rafaellehmkuhl/Bancada-Mitica-Parts-Models/Carrinho/Eixo Linear/Eixo_Linear_12mm.SLDPRT

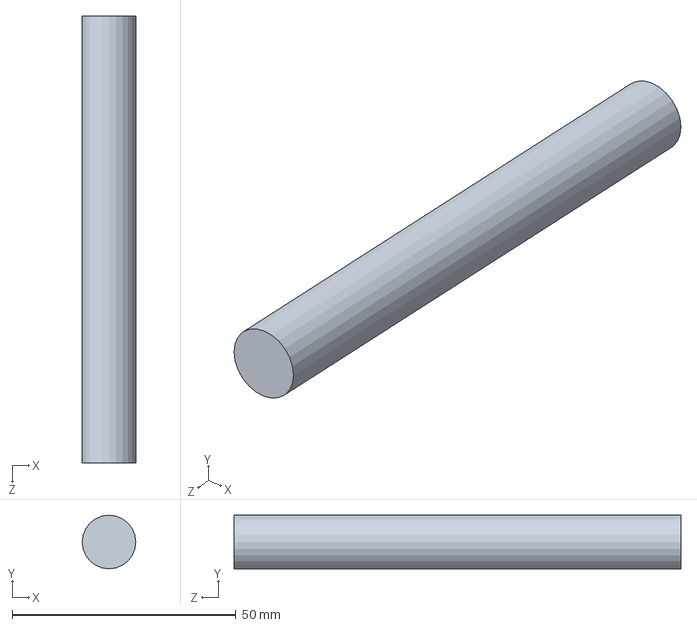
[picture p16: CAD file, 2018-05-09]
Carrinho/Eixo Linear/Eixo_Linear_12mm.SLDPRT
12.0 x 12.0 x 100.0 mm
