rafaellehmkuhl/Bancada-Mitica-Parts-Models/Carrinho/Pillow Block SC12UU/Adaptador_para_Pillow_Block_SC12UU.SLDPRT

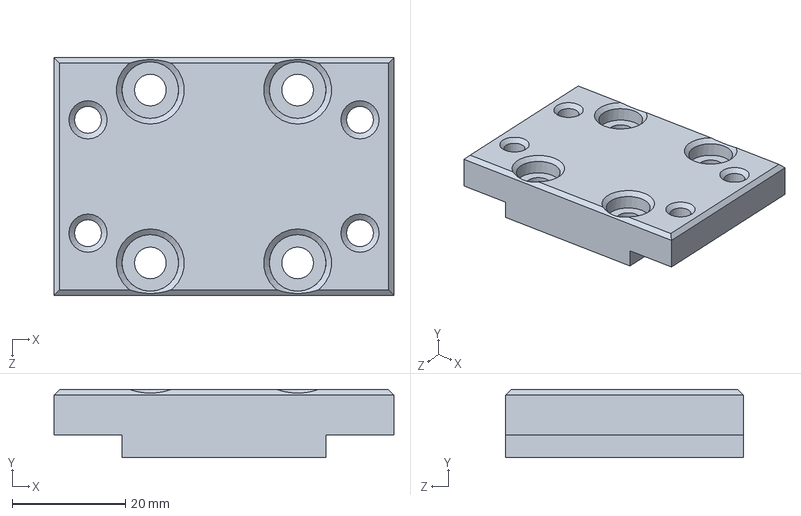
[picture p17: CAD file, 2018-05-09]
Carrinho/Pillow Block SC12UU/Adaptador_para_Pillow_Block_SC12UU.SLDPRT
60.0 x 12.0 x 42.0 mm
