rafaellehmkuhl/Bancada-Mitica-Parts-Models/Celula de carga/Encaixe_Celula - Teste de Ajuste.SLDPRT

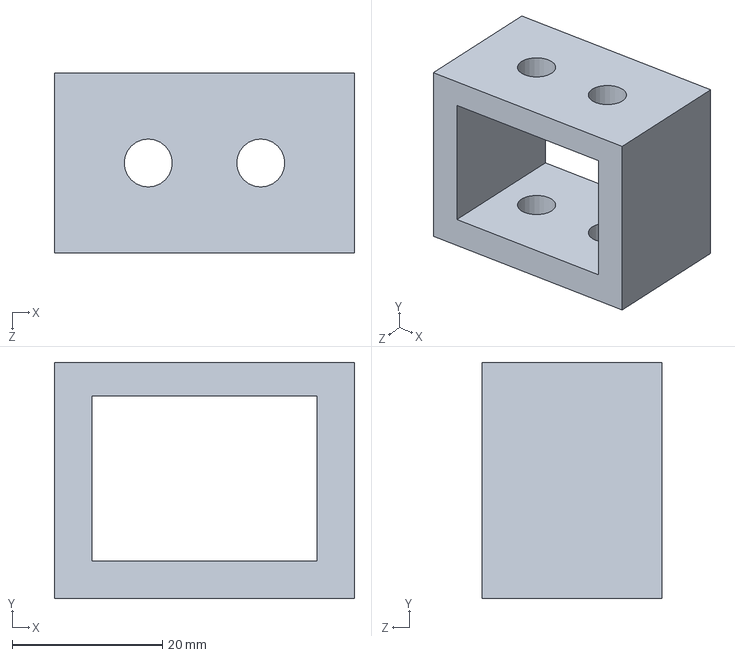
[picture p18: CAD file, 2018-07-06]
Celula de carga/Encaixe_Celula - Teste de Ajuste.SLDPRT
40.0 x 31.5 x 24.0 mm
