rafaellehmkuhl/Bancada-Mitica-Parts-Models/Celula de carga/EncaixeCelulaAnguloFixo/Encaixe_Celula_de_Angulo_Fixo.SLDPRT

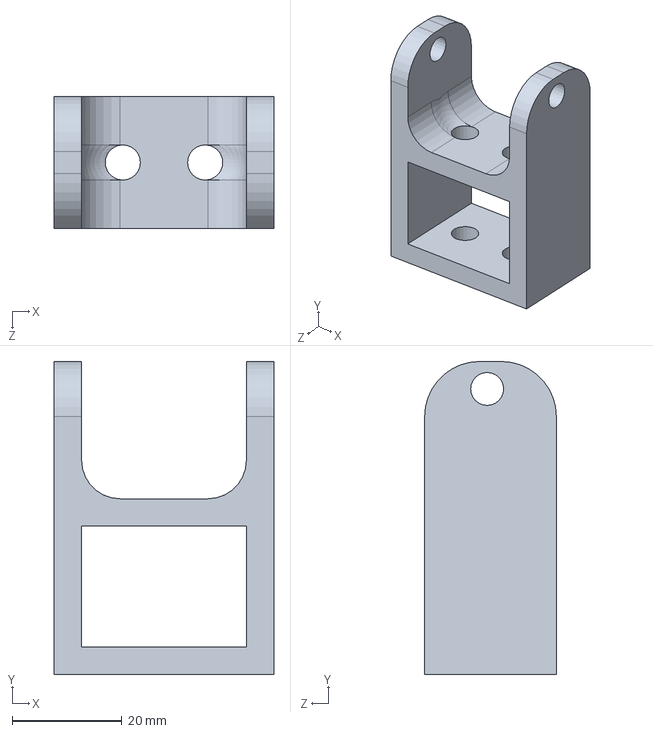
[picture p19: CAD file, 2018-07-06]
Celula de carga/EncaixeCelulaAnguloFixo/Encaixe_Celula_de_Angulo_Fixo.SLDPRT
40.0 x 57.0 x 24.0 mm
