rafaellehmkuhl/Bancada-Mitica-Parts-Models/Celula de carga/EncaixeCelulaAnguloVariavel/Peça_Central.sldprt

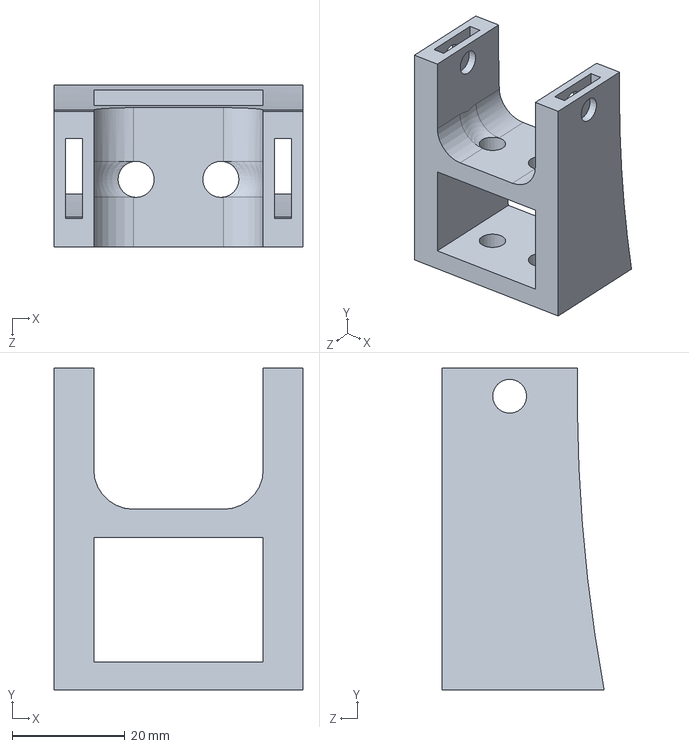
[picture p20: CAD file, 2018-07-06]
Celula de carga/EncaixeCelulaAnguloVariavel/Peça_Central.sldprt
44.0 x 57.0 x 28.7 mm
