rafaellehmkuhl/Bancada-Mitica-Parts-Models/Celula de carga/Suportes/Suporte_para_Celula_de_Carga_Reforcado_ajustavel.SLDPRT

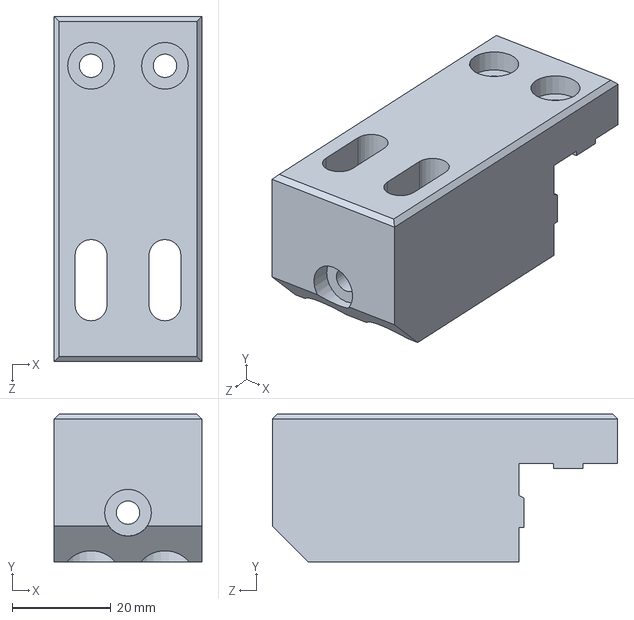
[picture p21: CAD file, 2018-07-06]
Celula de carga/Suportes/Suporte_para_Celula_de_Carga_Reforcado_ajustavel.SLDPRT
30.0 x 30.0 x 70.0 mm
