rafaellehmkuhl/Bancada-Mitica-Parts-Models/Conexoes/Antigos/AdaptadorSuporteSK12.SLDPRT

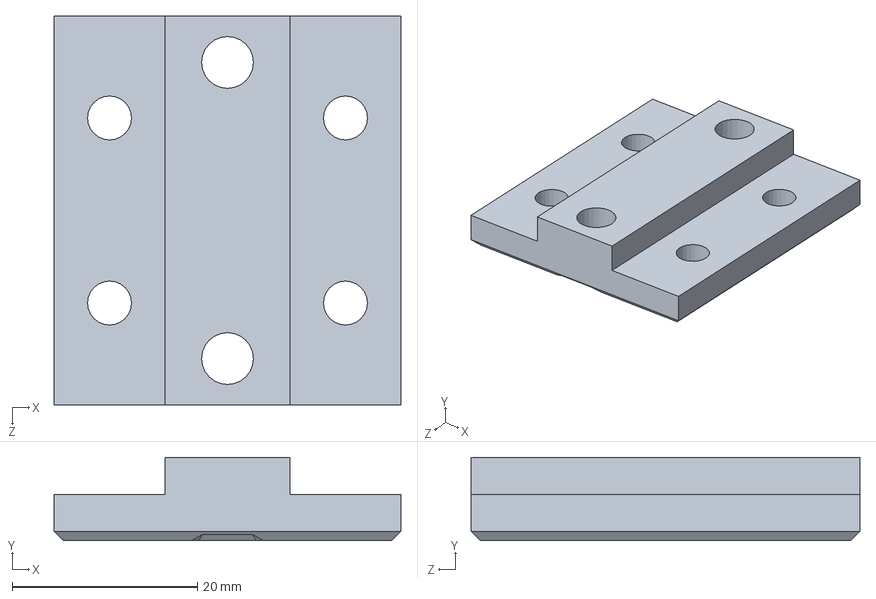
[picture p22: CAD file, 2018-04-30]
Conexoes/Antigos/AdaptadorSuporteSK12.SLDPRT
37.5 x 9.00 x 42.0 mm
