rafaellehmkuhl/Bancada-Mitica-Parts-Models/Conexoes/Cabo_de_aco.SLDPRT

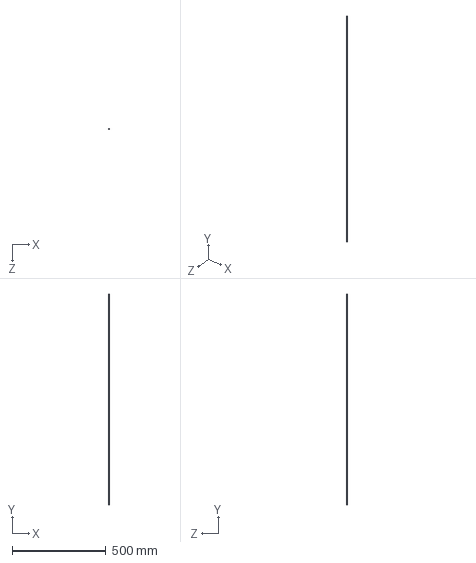
[picture p23: CAD file, 2018-05-29]
Conexoes/Cabo_de_aco.SLDPRT
6.00 x 1124.0 x 6.00 mm
