rafaellehmkuhl/Bancada-Mitica-Parts-Models/Conexoes/STLs/EncaixeDianteiroAsa.STL

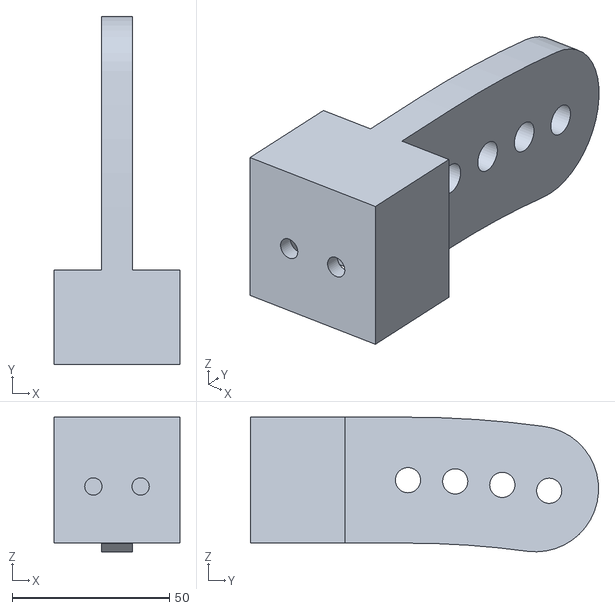
[picture p24: CAD file, 2018-07-06]
Conexoes/STLs/EncaixeDianteiroAsa.STL
40.0 x 110.5 x 42.7
