rafaellehmkuhl/Bancada-Mitica-Parts-Models/Perfis de Aluminio/Perfil_20x20mm.SLDPRT

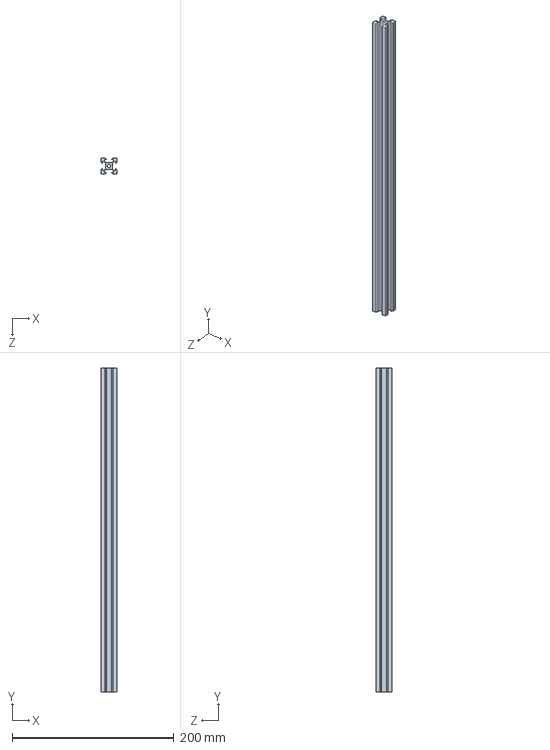
[picture p25: CAD file, 2018-05-29]
Perfis de Aluminio/Perfil_20x20mm.SLDPRT
20.0 x 400.0 x 20.0 mm
