rafaellehmkuhl/Bancada-Mitica-Parts-Models/Placas Eletronicas/Encaixe_PCBs.SLDPRT

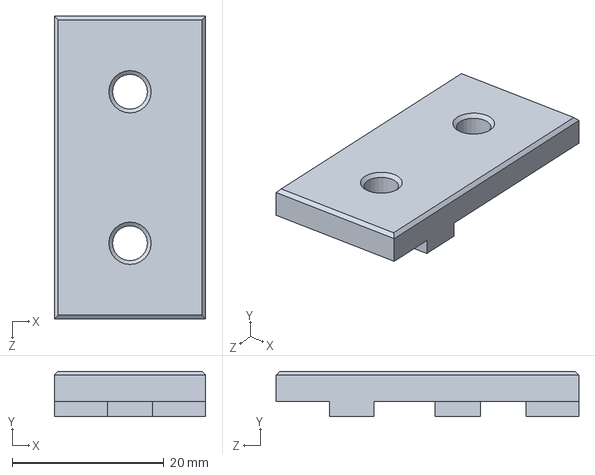
[picture p26: CAD file, 2018-04-30]
Placas Eletronicas/Encaixe_PCBs.SLDPRT
20.0 x 6.00 x 40.0 mm
