rafaellehmkuhl/Bancada-Mitica-Parts-Models/Calibraçao/Placa-asa/Abraçadeira/Abracadeira_Grampo_U_Placa_de_Calibracao_Argola.SLDPRT

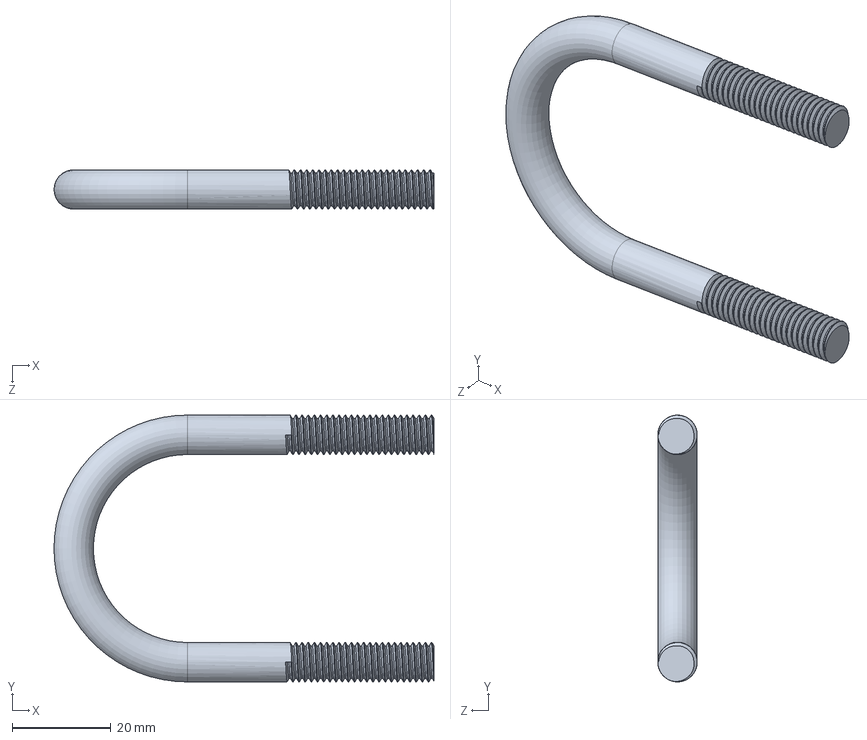
[picture p27: CAD file, 2018-07-06]
Calibraçao/Placa-asa/Abraçadeira/Abracadeira_Grampo_U_Placa_de_Calibracao_Argola.SLDPRT
77.1 x 54.1 x 8.00 mm
