rafaellehmkuhl/Bancada-Mitica-Parts-Models/Calibraçao/Placa-asa/Placa.SLDPRT

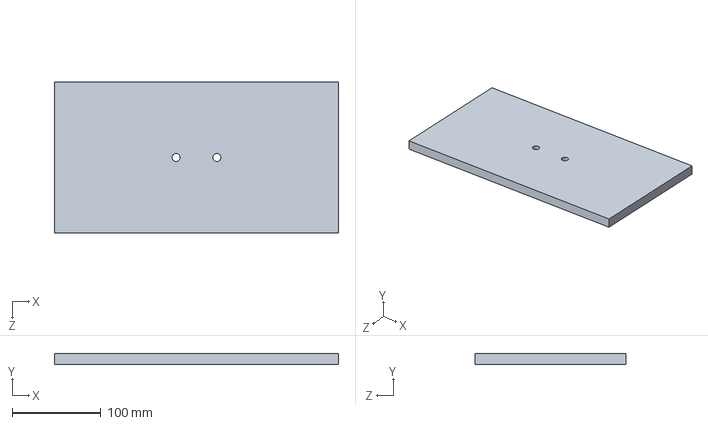
[picture p28: CAD file, 2018-07-06]
Calibraçao/Placa-asa/Placa.SLDPRT
320.0 x 12.0 x 170.0 mm
