rafaellehmkuhl/Bancada-Mitica-Parts-Models/Calibraçao/Roldana/Suporte_de_rolamento.SLDPRT

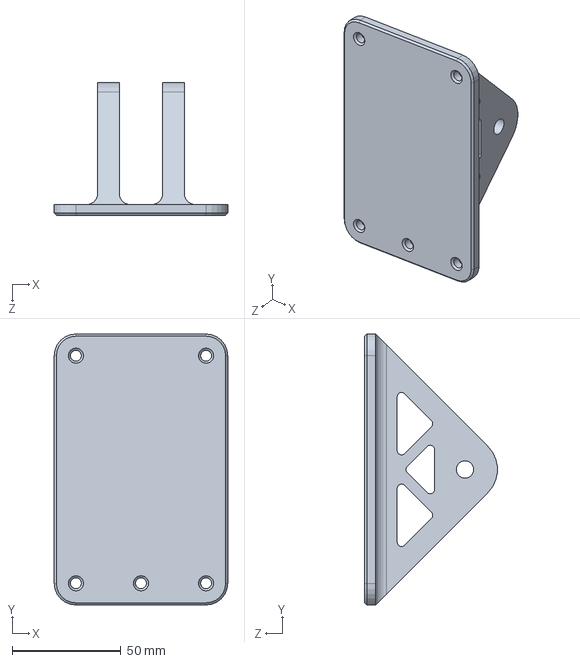
[picture p29: CAD file, 2018-05-29]
Calibraçao/Roldana/Suporte_de_rolamento.SLDPRT
80.0 x 124.9 x 61.1 mm
