rafaellehmkuhl/Bancada-Mitica-Parts-Models/Carrinho/Pillow Block SC12UU/Pillow_Block_SC12UU.SLDPRT

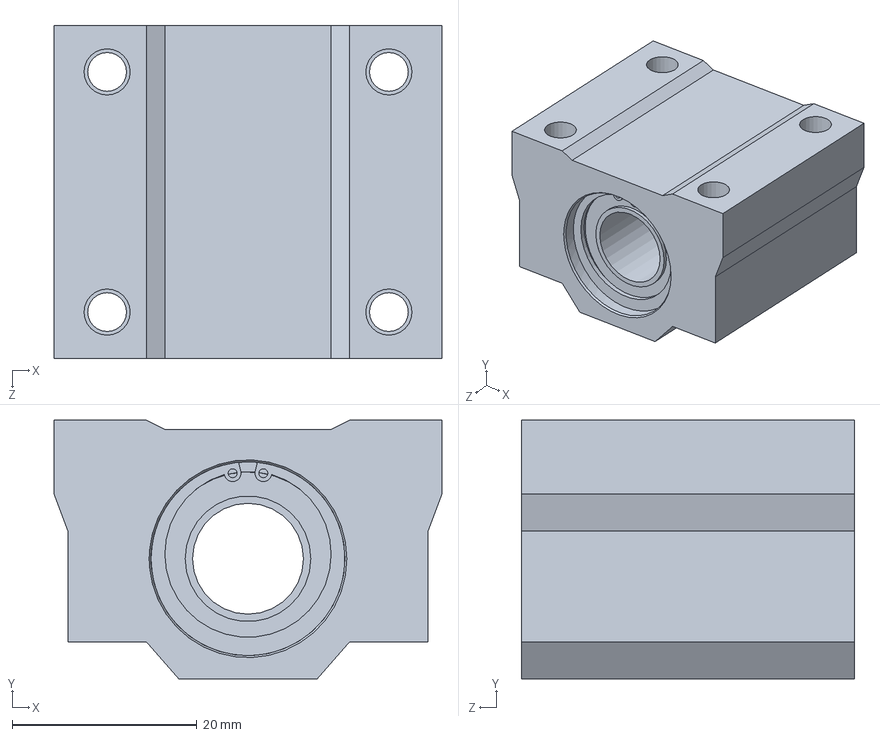
[picture p30: CAD file, 2018-05-09]
Carrinho/Pillow Block SC12UU/Pillow_Block_SC12UU.SLDPRT
42.0 x 28.0 x 36.0 mm
