rafaellehmkuhl/Bancada-Mitica-Parts-Models/Celula de carga/Celula_de_Carga_20kg.SLDPRT

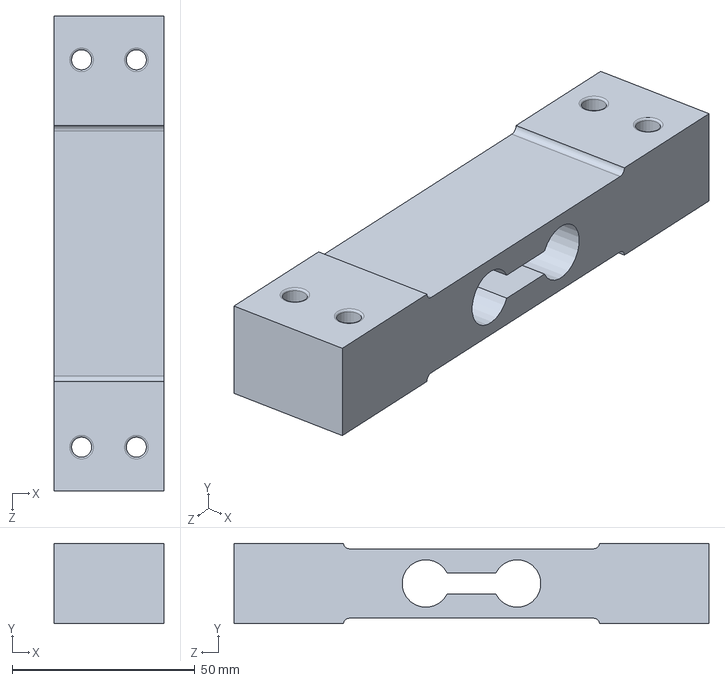
[picture p31: CAD file, 2018-05-09]
Celula de carga/Celula_de_Carga_20kg.SLDPRT
30.0 x 22.0 x 130.0 mm
