rafaellehmkuhl/Bancada-Mitica-Parts-Models/Celula de carga/EncaixeCelulaAnguloVariavel/Encaixe_Celula_de_Angulo_Variavel.SLDPRT

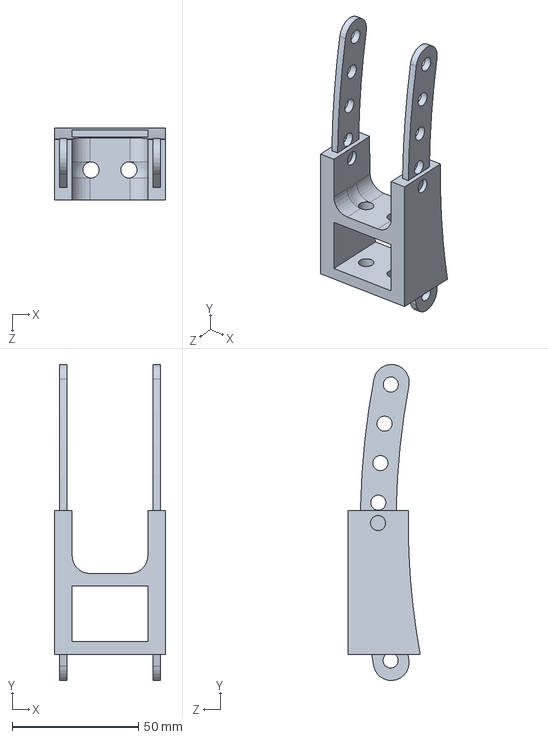
[picture p32: CAD file, 2018-07-06]
Celula de carga/EncaixeCelulaAnguloVariavel/Encaixe_Celula_de_Angulo_Variavel.SLDPRT
44.0 x 125.2 x 28.7 mm
