rafaellehmkuhl/Bancada-Mitica-Parts-Models/Celula de carga/Suportes/Suporte_para_Celula_de_Carga_Reforcado.SLDPRT

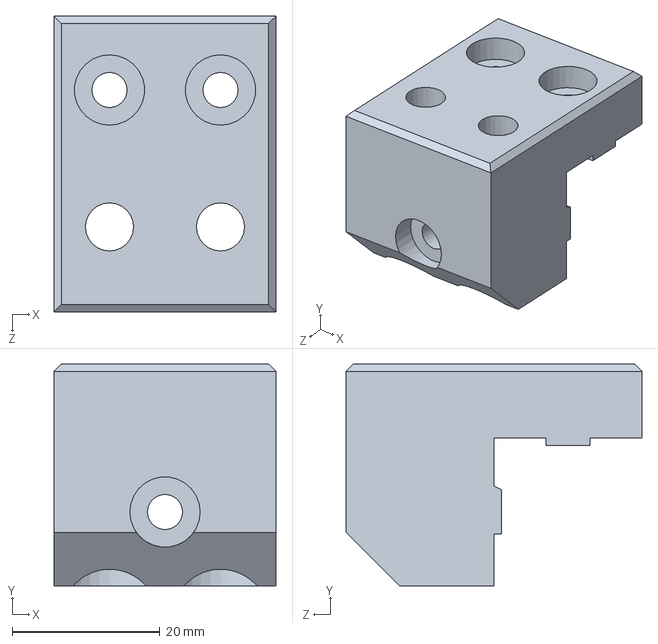
[picture p33: CAD file, 2018-05-09]
Celula de carga/Suportes/Suporte_para_Celula_de_Carga_Reforcado.SLDPRT
30.0 x 30.0 x 40.0 mm
