rafaellehmkuhl/Bancada-Mitica-Parts-Models/Conexoes/Antigos/Placa_lateral_90.SLDPRT

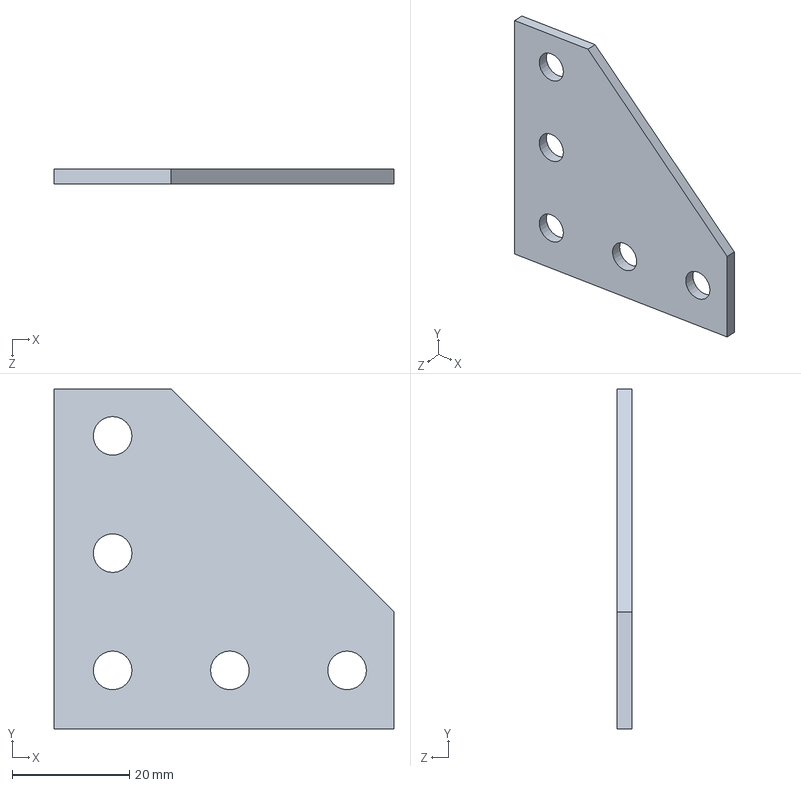
[picture p34: CAD file, 2018-04-30]
Conexoes/Antigos/Placa_lateral_90.SLDPRT
58.0 x 58.0 x 2.50 mm
