rafaellehmkuhl/Bancada-Mitica-Parts-Models/Conexoes/Parafuso_Olhal_30mm.SLDPRT

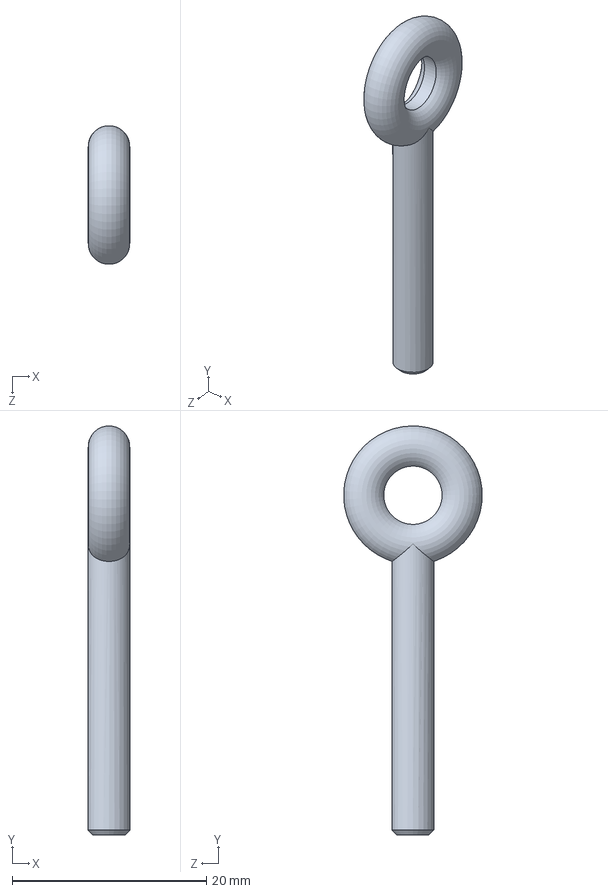
[picture p35: CAD file, 2018-05-29]
Conexoes/Parafuso_Olhal_30mm.SLDPRT
4.30 x 42.1 x 14.3 mm
