rafaellehmkuhl/Bancada-Mitica-Parts-Models/Conexoes/STLs/Placa_lateral_45.STL

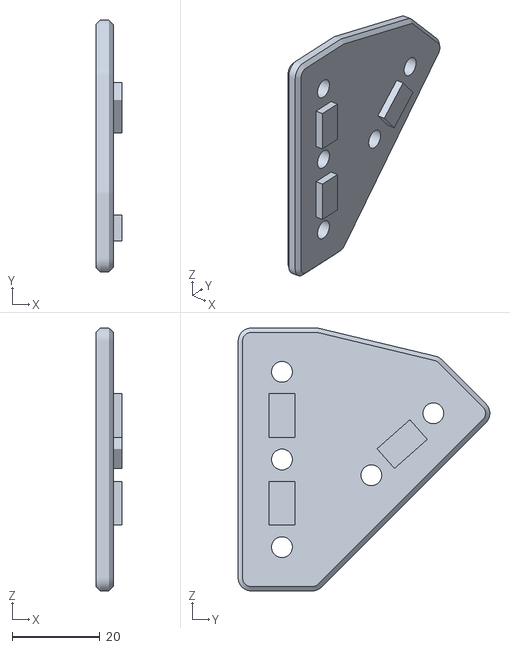
[picture p36: CAD file, 2018-04-30]
Conexoes/STLs/Placa_lateral_45.STL
6.00 x 57.4 x 60.0
