rafaellehmkuhl/Bancada-Mitica-Parts-Models/Perfis de Aluminio/Perfil_20x40mm.SLDPRT

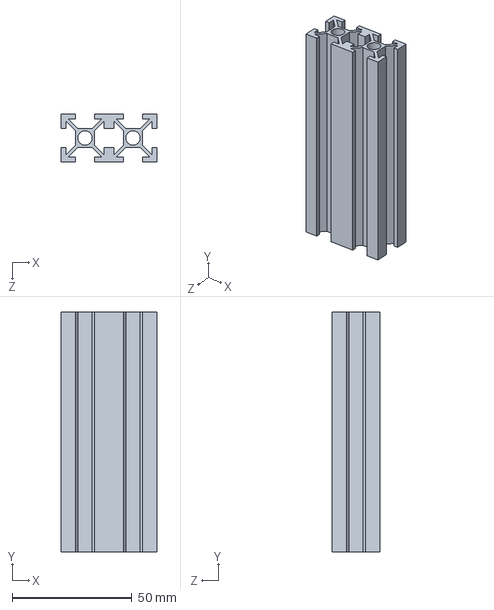
[picture p37: CAD file, 2018-05-09]
Perfis de Aluminio/Perfil_20x40mm.SLDPRT
40.0 x 100.0 x 20.0 mm
