rafaellehmkuhl/Bancada-Mitica-Parts-Models/Placas Eletronicas/Case_Celulas.SLDPRT

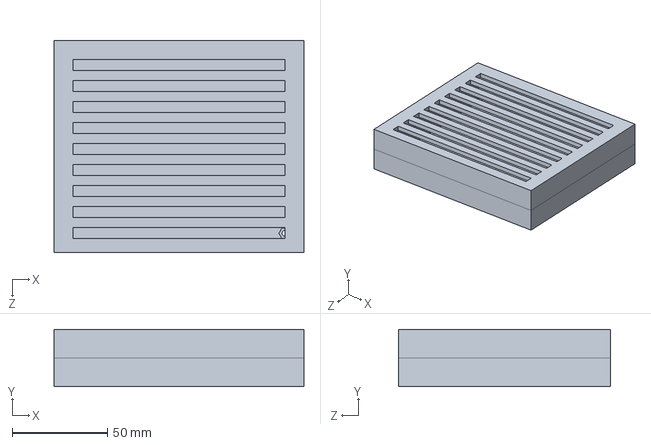
[picture p38: CAD file, 2018-04-30]
Placas Eletronicas/Case_Celulas.SLDPRT
131.0 x 30.0 x 111.0 mm
