rafaellehmkuhl/Bancada-Mitica-Parts-Models/Calibraçao/Placa-asa/Vareta6mm.SLDPRT

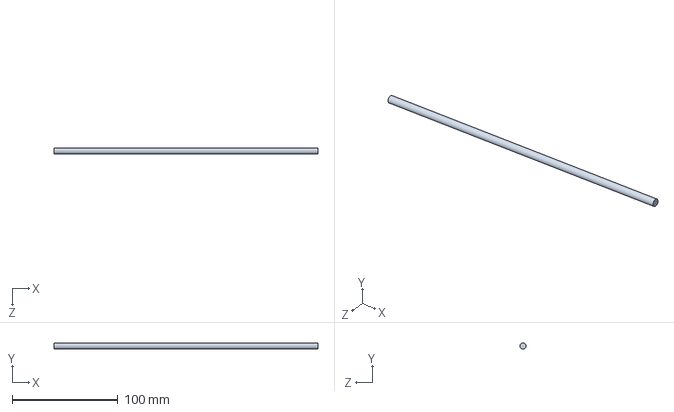
[picture p39: CAD file, 2018-07-06]
Calibraçao/Placa-asa/Vareta6mm.SLDPRT
250.0 x 6.00 x 6.00 mm
