rafaellehmkuhl/Bancada-Mitica-Parts-Models/Calibraçao/Roldana/608RS.SLDPRT

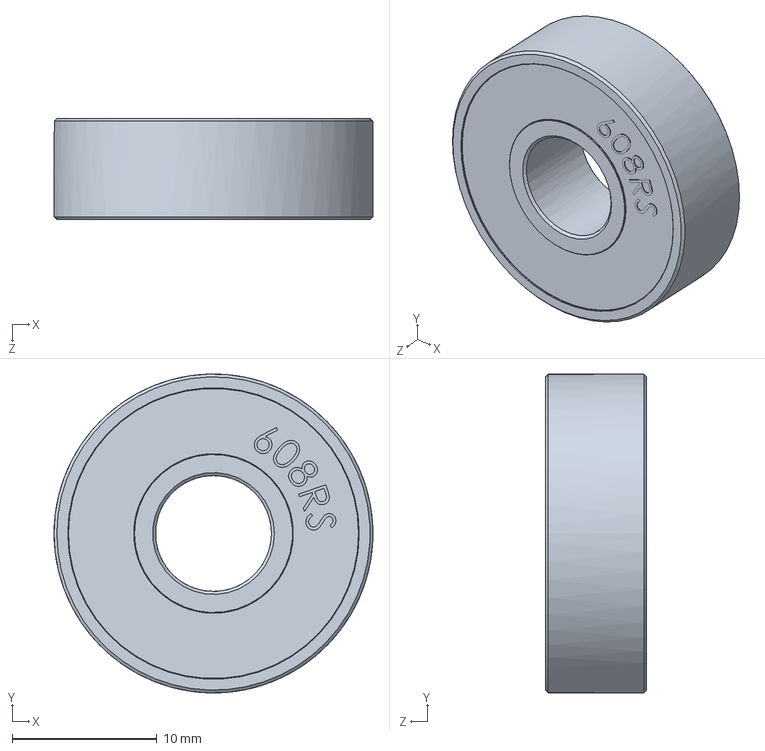
[picture p40: CAD file, 2018-05-29]
Calibraçao/Roldana/608RS.SLDPRT
22.0 x 22.0 x 7.00 mm
