rafaellehmkuhl/Bancada-Mitica-Parts-Models/Conexoes/Antigos/Placa_de_conexao_celula_de_carga.SLDPRT

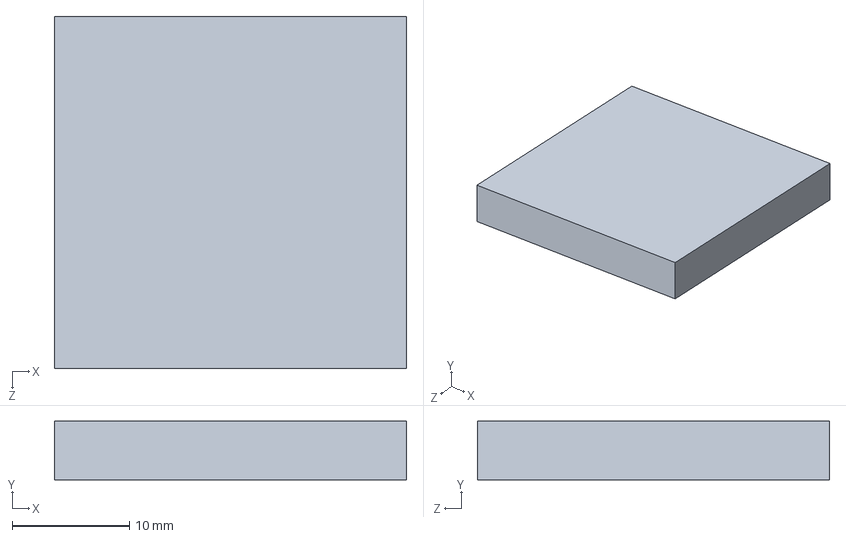
[picture p41: CAD file, 2018-04-30]
Conexoes/Antigos/Placa_de_conexao_celula_de_carga.SLDPRT
30.0 x 5.00 x 30.0 mm
