rafaellehmkuhl/Bancada-Mitica-Parts-Models/Conexoes/Cantoneira_interna_20x20mm.SLDPRT

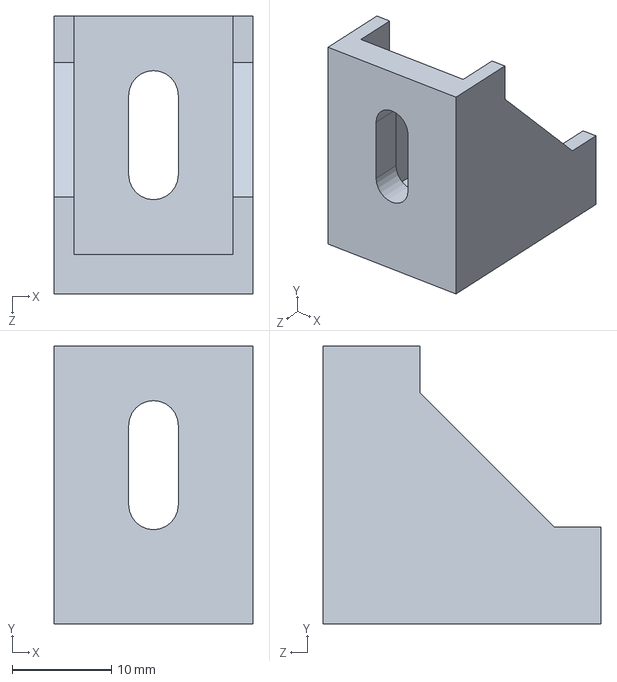
[picture p42: CAD file, 2018-05-09]
Conexoes/Cantoneira_interna_20x20mm.SLDPRT
20.0 x 28.0 x 28.0 mm
