rafaellehmkuhl/Bancada-Mitica-Parts-Models/Placas Eletronicas/Encaixe_PCBs_2.SLDPRT

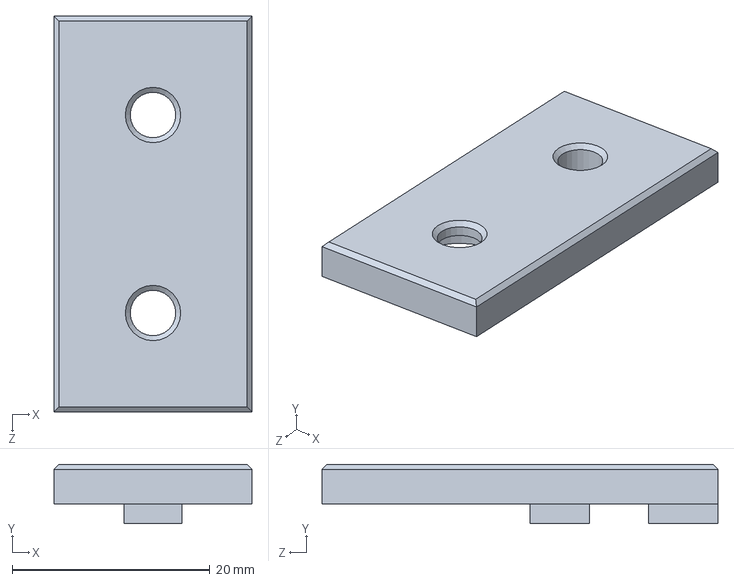
[picture p43: CAD file, 2018-04-30]
Placas Eletronicas/Encaixe_PCBs_2.SLDPRT
20.0 x 6.00 x 40.0 mm
