rafaellehmkuhl/Bancada-Mitica-Parts-Models/Calibraçao/Roldana/Encaixe_corda.SLDPRT

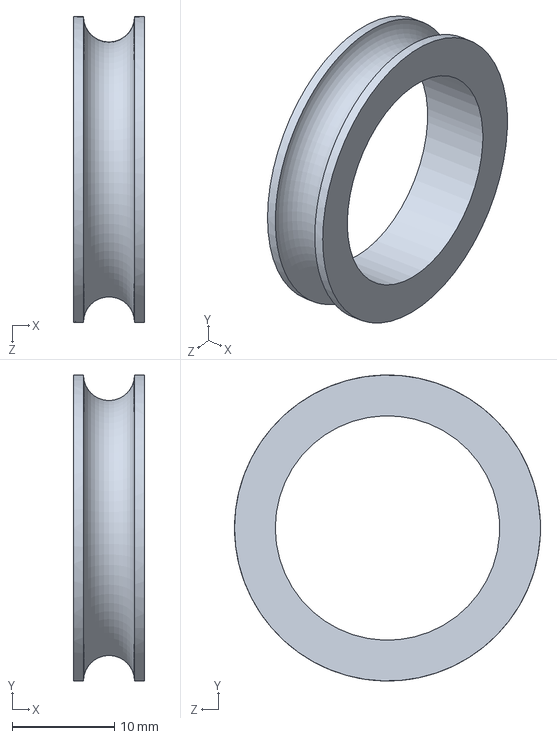
[picture p44: CAD file, 2018-05-29]
Calibraçao/Roldana/Encaixe_corda.SLDPRT
7.00 x 30.0 x 30.0 mm
