rafaellehmkuhl/Bancada-Mitica-Parts-Models/Carrinho/Pillow Block SC12UU/Rolamento_Linear_LM12UU.SLDPRT

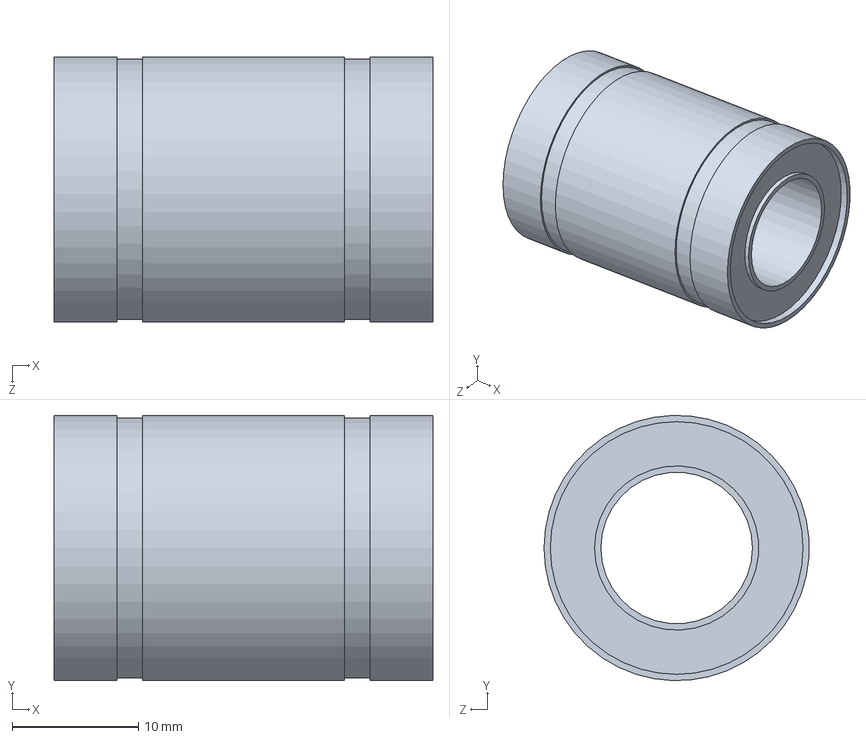
[picture p45: CAD file, 2018-04-30]
Carrinho/Pillow Block SC12UU/Rolamento_Linear_LM12UU.SLDPRT
30.0 x 21.0 x 21.0 mm
