rafaellehmkuhl/Bancada-Mitica-Parts-Models/Celula de carga/EncaixeCelulaAnguloVariavel/Peça_de_angulo.sldprt

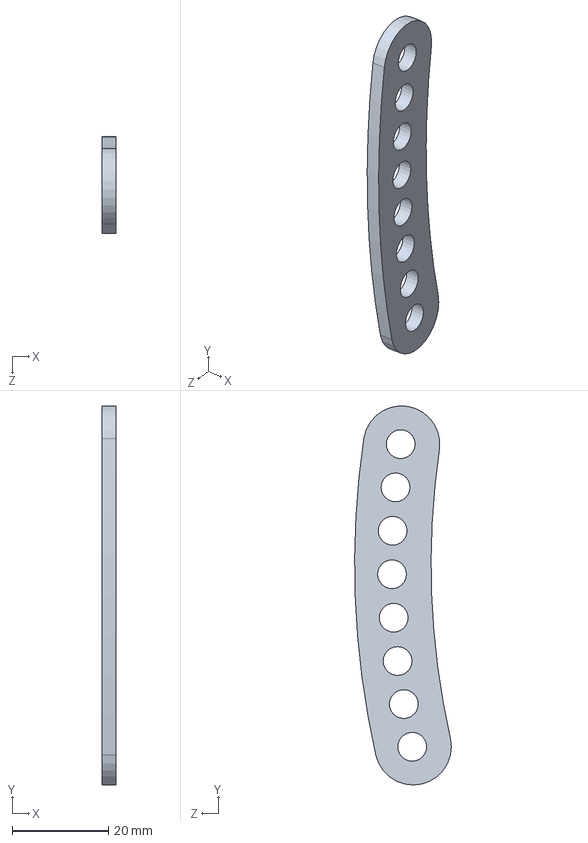
[picture p46: CAD file, 2018-07-06]
Celula de carga/EncaixeCelulaAnguloVariavel/Peça_de_angulo.sldprt
3.00 x 78.9 x 20.1 mm
