rafaellehmkuhl/Bancada-Mitica-Parts-Models/Conexoes/Antigos/Placa_lateral_baixo.SLDPRT

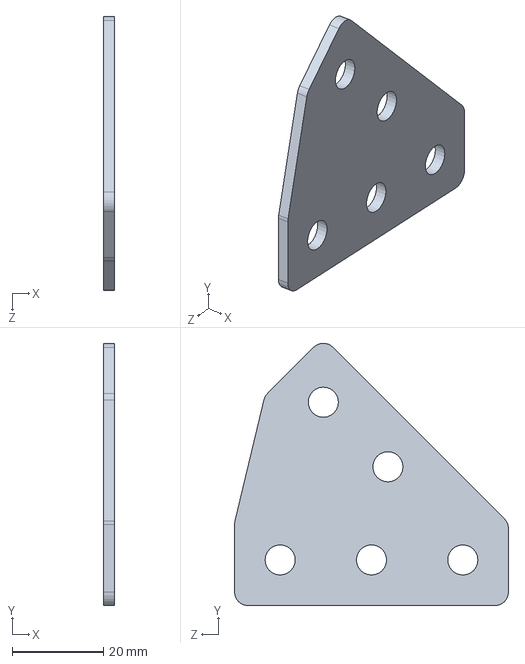
[picture p47: CAD file, 2018-04-30]
Conexoes/Antigos/Placa_lateral_baixo.SLDPRT
2.50 x 57.4 x 60.0 mm
