rafaellehmkuhl/Bancada-Mitica-Parts-Models/Calibraçao/Placa-asa/Encaixe_Placa_de_Calibracao.SLDPRT

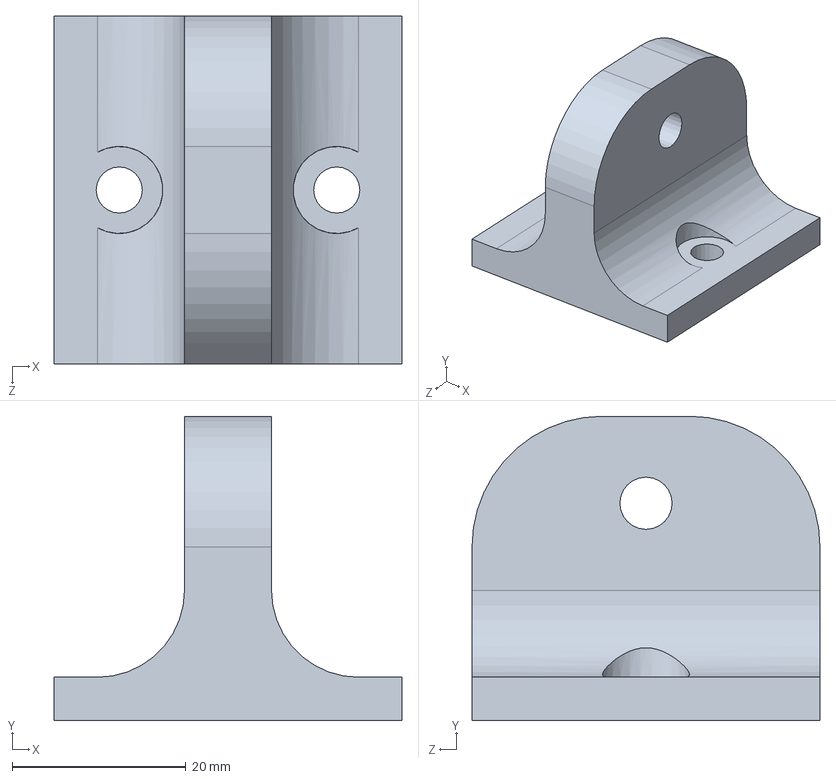
[picture p48: CAD file, 2018-07-06]
Calibraçao/Placa-asa/Encaixe_Placa_de_Calibracao.SLDPRT
40.0 x 35.0 x 40.0 mm
