rafaellehmkuhl/Bancada-Mitica-Parts-Models/Calibraçao/Roldana/Suporte_de_roldana.SLDPRT

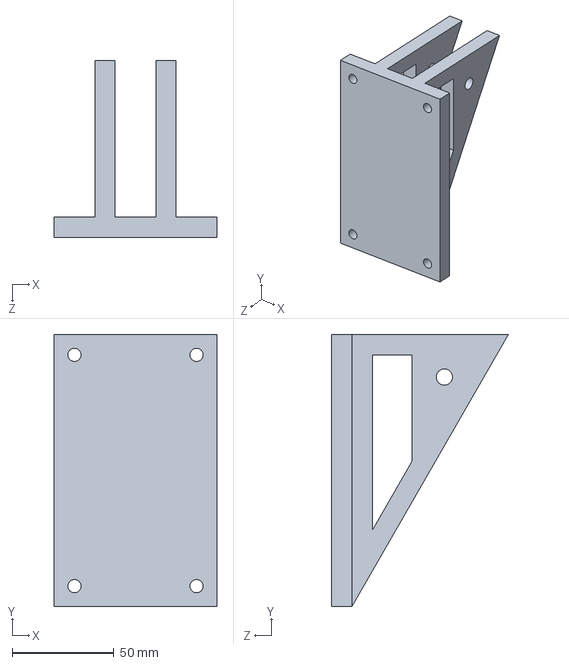
[picture p49: CAD file, 2018-05-29]
Calibraçao/Roldana/Suporte_de_roldana.SLDPRT
80.0 x 133.6 x 86.9 mm
