rafaellehmkuhl/Bancada-Mitica-Parts-Models/Conexoes/Antigos/Placa_de_conexao_celula_de_carga_2.SLDPRT

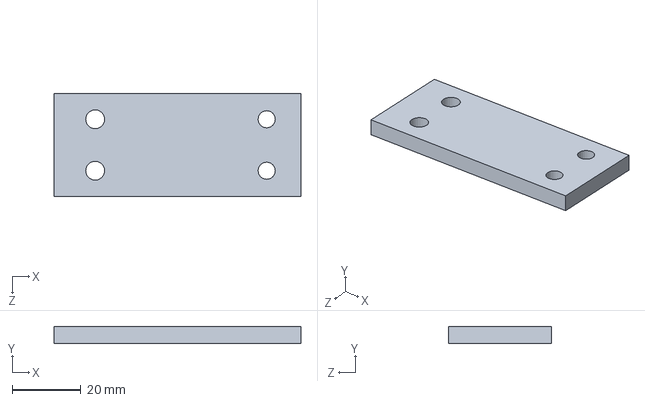
[picture p50: CAD file, 2018-04-30]
Conexoes/Antigos/Placa_de_conexao_celula_de_carga_2.SLDPRT
72.0 x 5.00 x 30.0 mm
