rafaellehmkuhl/Bancada-Mitica-Parts-Models/Calibraçao/Roldana/Espaçador_rolamento.SLDPRT

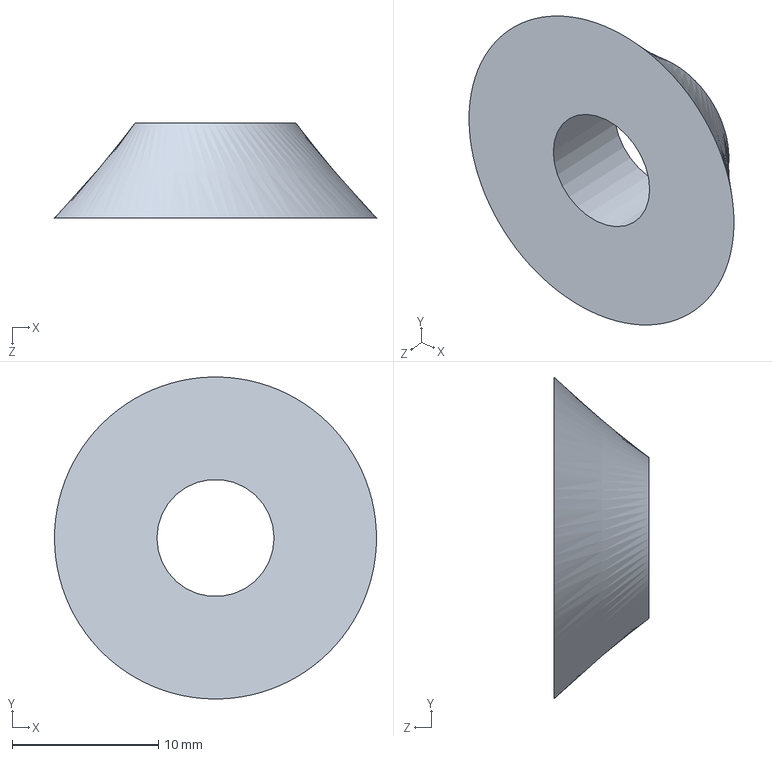
[picture p51: CAD file, 2018-05-29]
Calibraçao/Roldana/Espaçador_rolamento.SLDPRT
22.0 x 22.0 x 6.50 mm
