rafaellehmkuhl/Bancada-Mitica-Parts-Models/Carrinho/Suporte de Eixo SK12/Shaft support SK12.SLDPRT

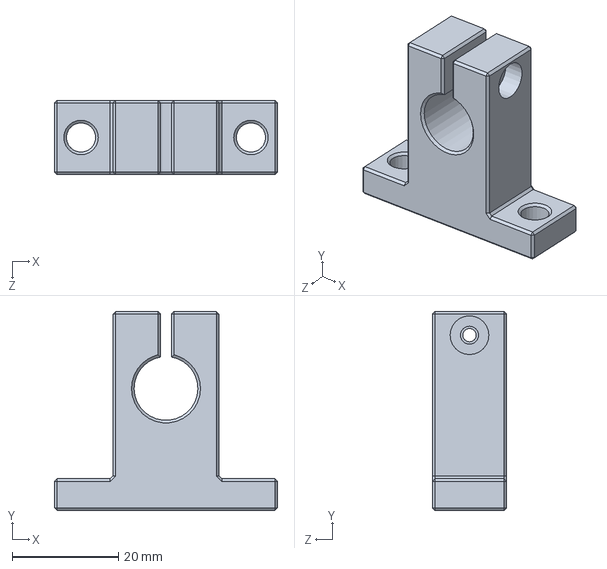
[picture p52: CAD file, 2018-05-09]
Carrinho/Suporte de Eixo SK12/Shaft support SK12.SLDPRT
42.0 x 37.5 x 14.0 mm
