rafaellehmkuhl/Bancada-Mitica-Parts-Models/Conexoes/Antigos/SuporteCelulaCarga.SLDPRT

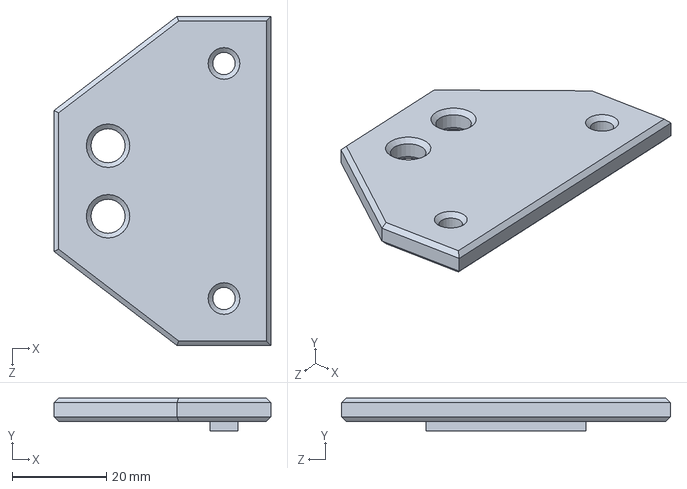
[picture p53: CAD file, 2018-04-30]
Conexoes/Antigos/SuporteCelulaCarga.SLDPRT
46.2 x 7.00 x 70.0 mm
