rafaellehmkuhl/Bancada-Mitica-Parts-Models/Conexoes/Cantoneira_plana_lateral.SLDPRT

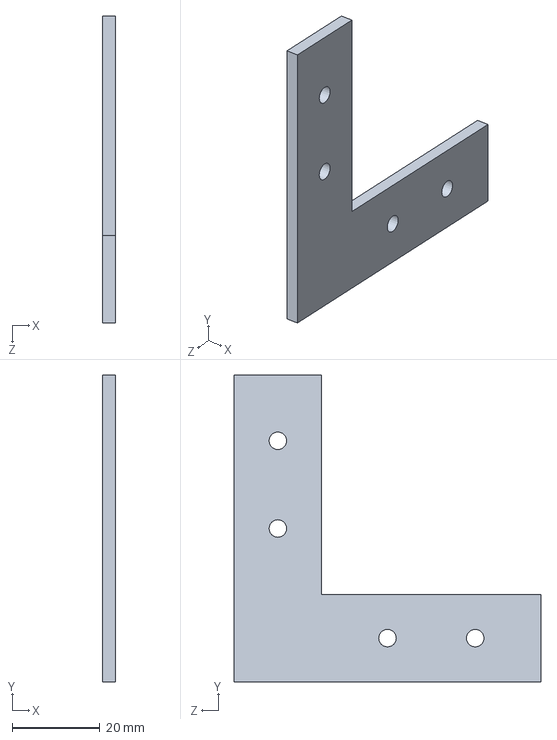
[picture p54: CAD file, 2018-05-09]
Conexoes/Cantoneira_plana_lateral.SLDPRT
3.00 x 70.0 x 70.0 mm
