rafaellehmkuhl/Bancada-Mitica-Parts-Models/Calibraçao/Roldana/Eixo_rolamento.SLDPRT

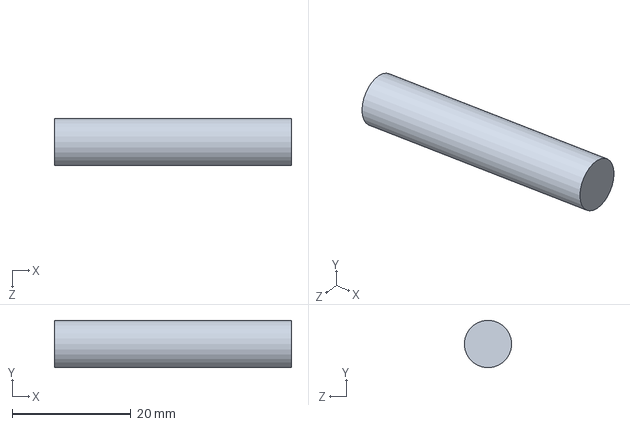
[picture p55: CAD file, 2018-05-29]
Calibraçao/Roldana/Eixo_rolamento.SLDPRT
40.0 x 8.00 x 8.00 mm
